AEFeinstein/Super-2020-Swadge-HW/hardware/kicad-libs/package3d/js202011cqn.stp

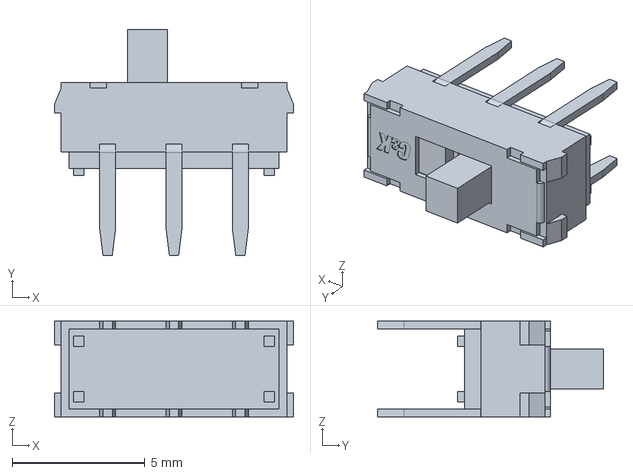
[picture p16: CAD file, 2019-01-19]
hardware/kicad-libs/package3d/js202011cqn.stp
9.00 x 8.50 x 3.60 mm
