AEFeinstein/Super-2020-Swadge-HW/hardware/kicad-libs/package3d/oled - Copy.FCStd

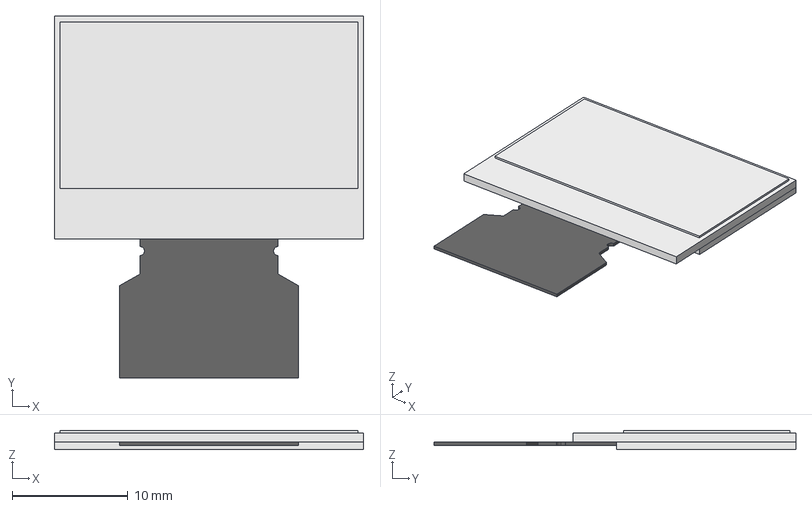
[picture p17: CAD file, 2019-08-31, an earlier design]
hardware/kicad-libs/package3d/oled - Copy.FCStd
26.7 x 31.3 x 1.65 mm
Polarizer
Panel
Cap
